pnamunn/Lunabotics/CAD/HADES CAD/Chassis/Copy of Motor Casing Bottom.SLDPRT

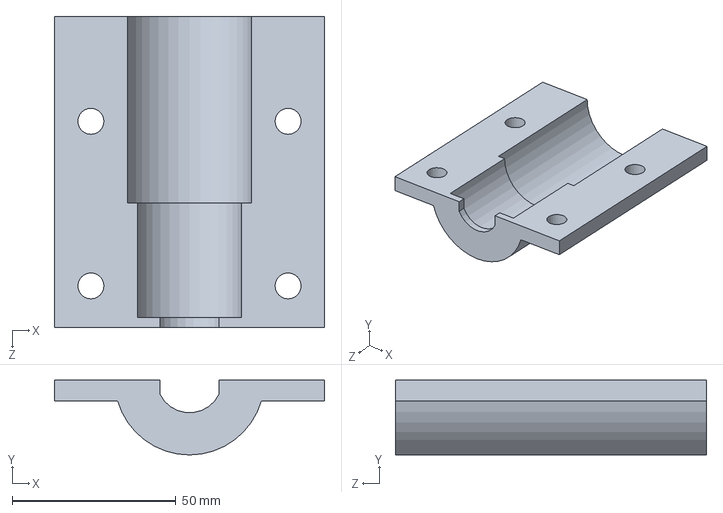
[picture p14: CAD file, 2023-11-08]
CAD/HADES CAD/Chassis/Copy of Motor Casing Bottom.SLDPRT
82.5 x 22.9 x 94.9 mm
