pnamunn/Lunabotics/CAD/HADES CAD/Excavation/Acuator Sleeve.SLDPRT

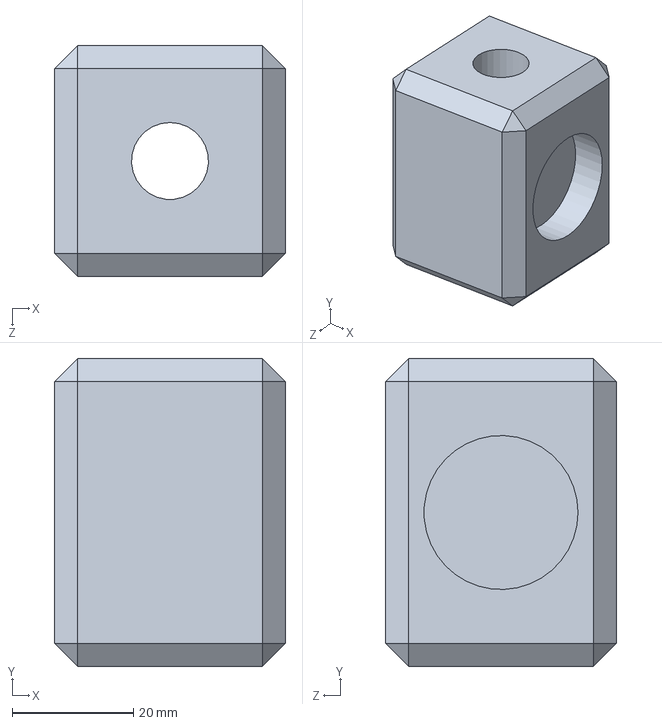
[picture p15: CAD file, 2023-11-08]
CAD/HADES CAD/Excavation/Acuator Sleeve.SLDPRT
38.1 x 50.8 x 38.1 mm
