pnamunn/Lunabotics/CAD/Wield Excavation Trial/2ft-9056K512_Multipurpose 6061 Aluminum Round Tube.SLDPRT

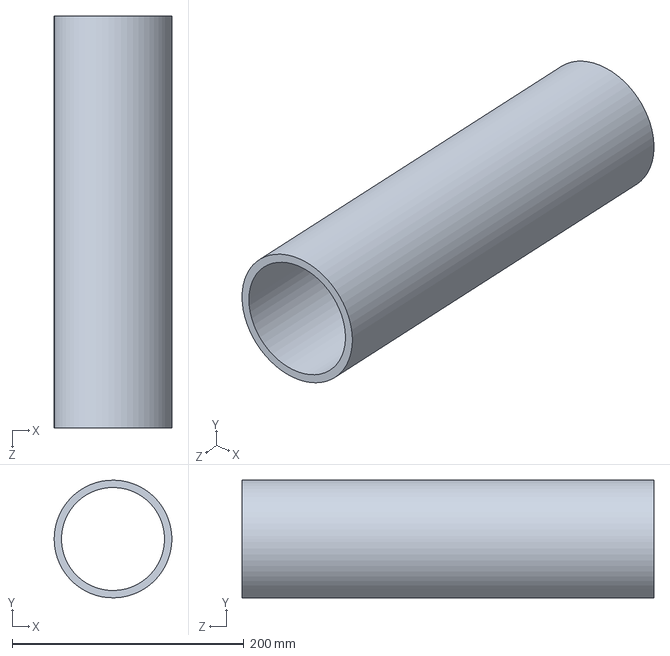
[picture p16: CAD file, 2023-11-10]
CAD/Wield Excavation Trial/2ft-9056K512_Multipurpose 6061 Aluminum Round Tube.SLDPRT
101.6 x 101.6 x 355.6 mm
