pnamunn/Lunabotics/CAD/GrouserWheel/Grouser.SLDPRT

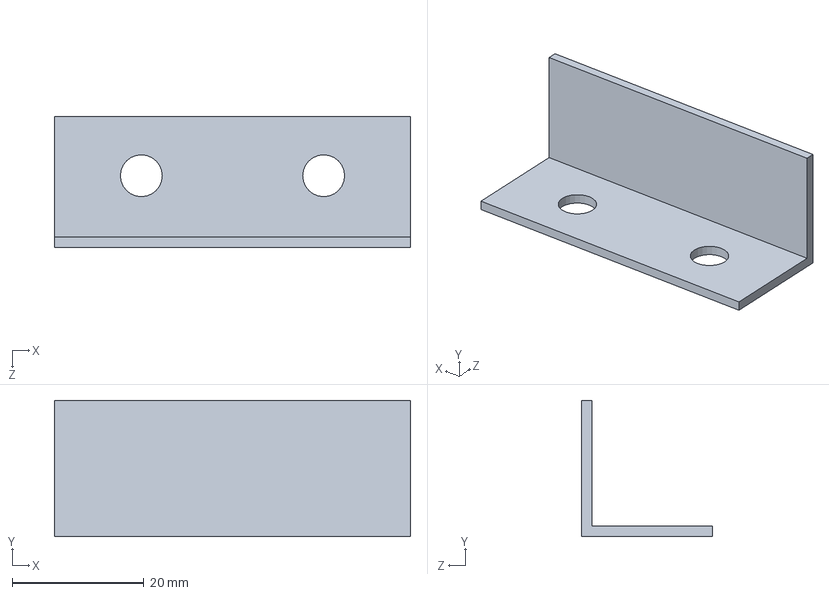
[picture p17: CAD file, 2023-10-27]
CAD/GrouserWheel/Grouser.SLDPRT
54.0 x 20.6 x 19.8 mm
