pnamunn/Lunabotics/CAD/HADES CAD/Excavation/Fixed Rod Seperator.SLDPRT

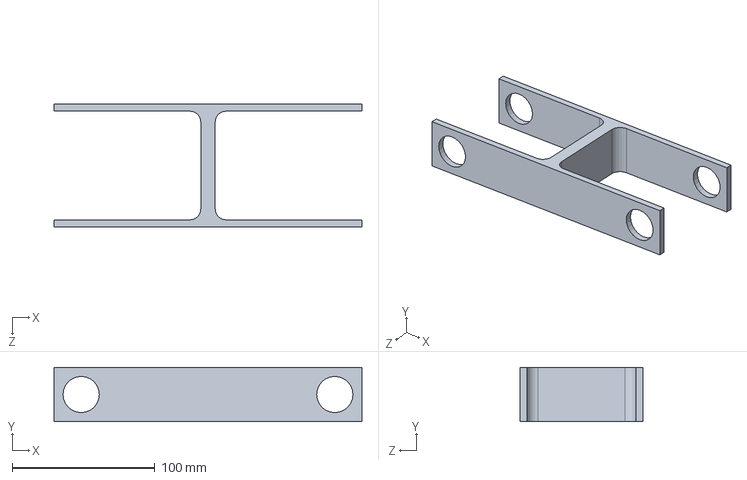
[picture p18: CAD file, 2023-11-08]
CAD/HADES CAD/Excavation/Fixed Rod Seperator.SLDPRT
215.9 x 38.1 x 86.4 mm
