pnamunn/Lunabotics/CAD/GrouserWheel/18Grouser Wheel/Grouser Wheel 20Degree.SLDPRT

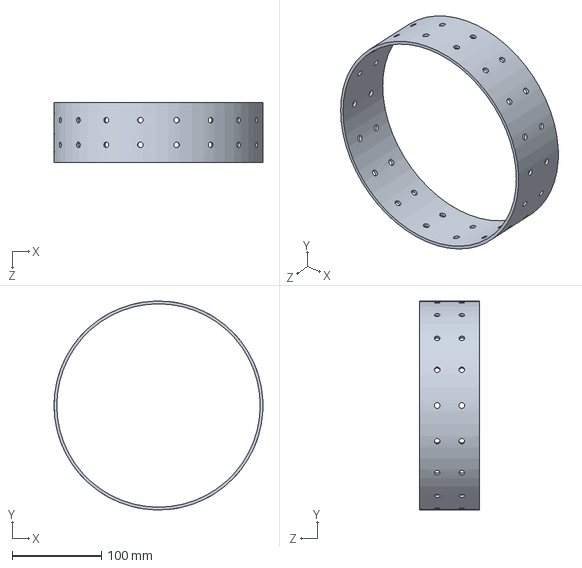
[picture p19: CAD file, 2023-11-10]
CAD/GrouserWheel/18Grouser Wheel/Grouser Wheel 20Degree.SLDPRT
233.8 x 233.7 x 66.7 mm
