pnamunn/Lunabotics/CAD/HADES CAD/Excavation/scoop.SLDPRT

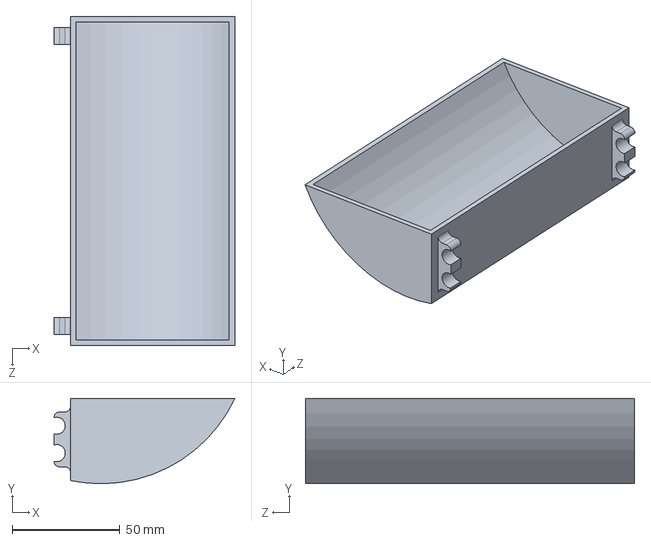
[picture p20: CAD file, 2023-11-08]
CAD/HADES CAD/Excavation/scoop.SLDPRT
83.8 x 39.5 x 152.4 mm
