pnamunn/Lunabotics/CAD/GrouserWheel/18Grouser Wheel/Wheel Mount.SLDPRT

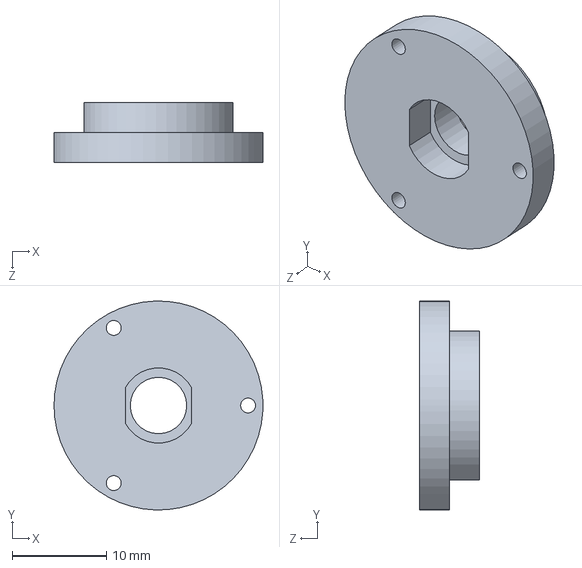
[picture p21: CAD file, 2023-10-27]
CAD/GrouserWheel/18Grouser Wheel/Wheel Mount.SLDPRT
22.2 x 22.2 x 6.36 mm
