pnamunn/Lunabotics/CAD/HADES CAD/Deposition/Deposition Spill Chute.SLDPRT

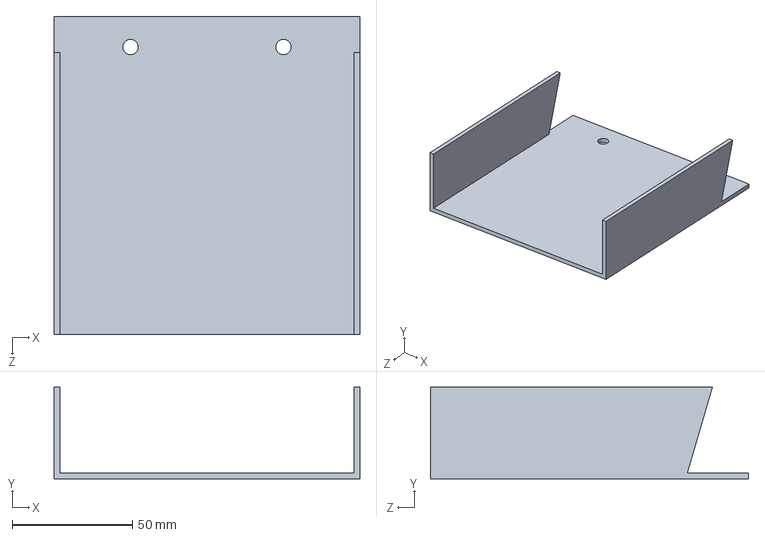
[picture p22: CAD file, 2023-11-08]
CAD/HADES CAD/Deposition/Deposition Spill Chute.SLDPRT
127.0 x 38.1 x 132.1 mm
