pnamunn/Lunabotics/CAD/HADES CAD/Drivetrain/Spoke_Standoff.SLDPRT

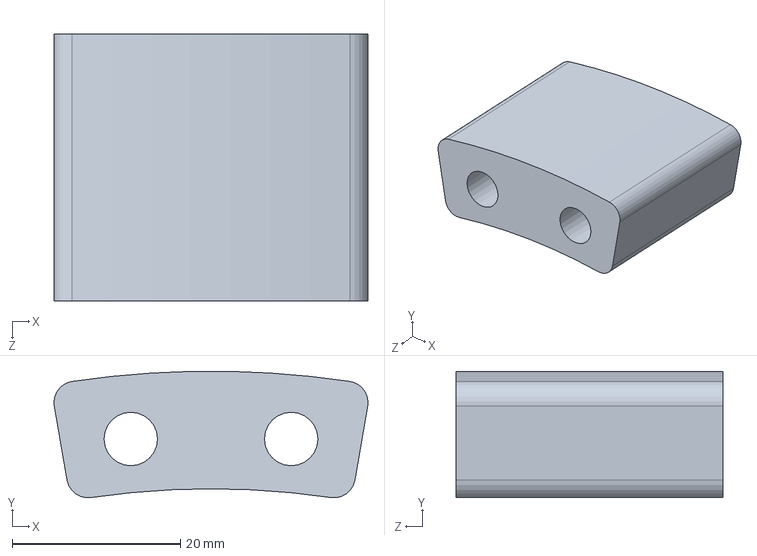
[picture p23: CAD file, 2023-11-08]
CAD/HADES CAD/Drivetrain/Spoke_Standoff.SLDPRT
37.3 x 15.0 x 31.8 mm
