pnamunn/Lunabotics/CAD/HADES CAD/Excavation/Side_Panel.SLDPRT

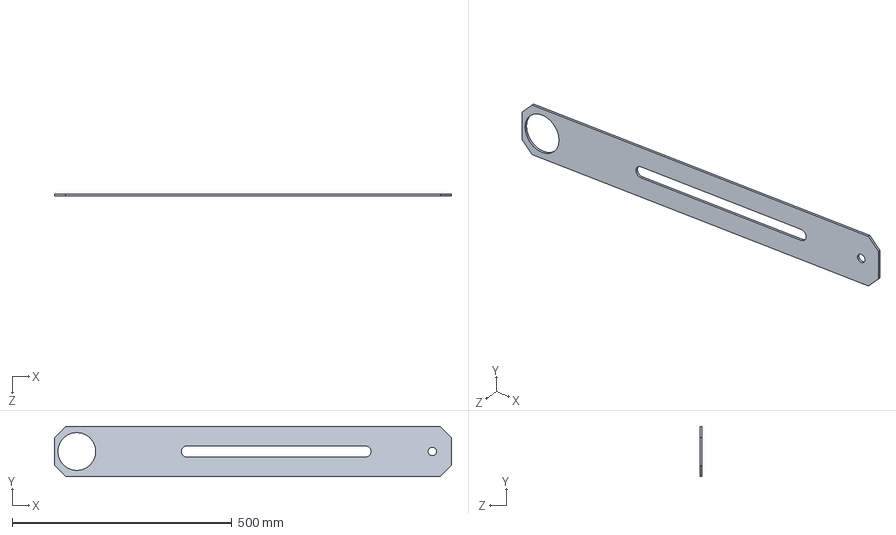
[picture p24: CAD file, 2023-11-08]
CAD/HADES CAD/Excavation/Side_Panel.SLDPRT
904.2 x 114.3 x 5.08 mm
