pnamunn/Lunabotics/CAD/GrouserWheel/18Grouser Wheel/MotorForWheel.SLDPRT

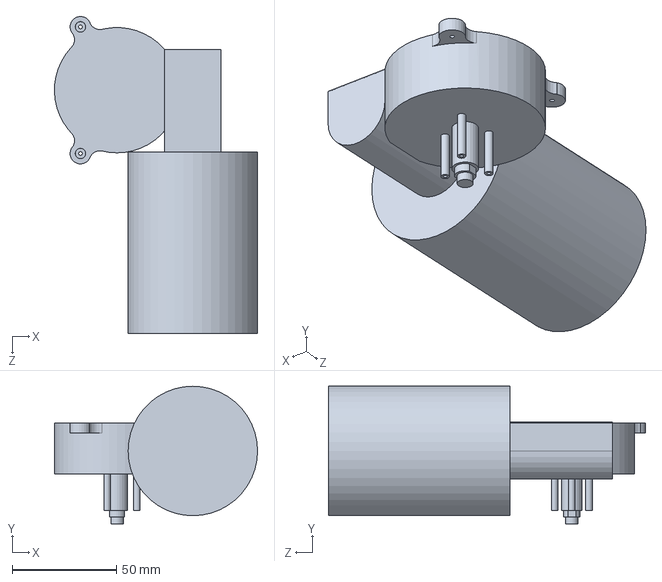
[picture p25: CAD file, 2023-10-27]
CAD/GrouserWheel/18Grouser Wheel/MotorForWheel.SLDPRT
97.3 x 65.9 x 151.8 mm
