pnamunn/Lunabotics/CAD/HADES CAD/Excavation/Fixing Rod.SLDPRT

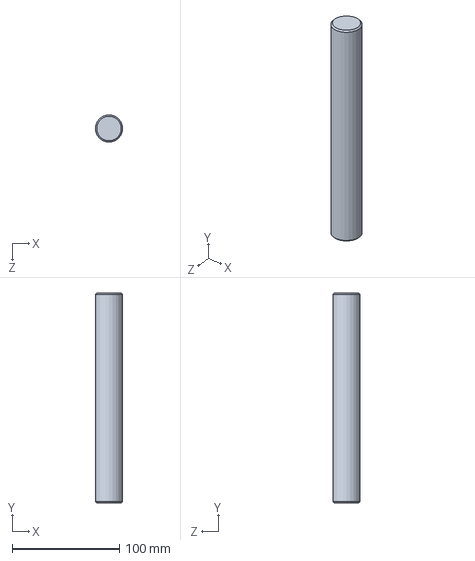
[picture p26: CAD file, 2023-11-08]
CAD/HADES CAD/Excavation/Fixing Rod.SLDPRT
25.4 x 195.6 x 25.4 mm
