pnamunn/Lunabotics/CAD/HADES CAD/Chassis/Copy of 47065T149_T-Slotted Framing.SLDPRT

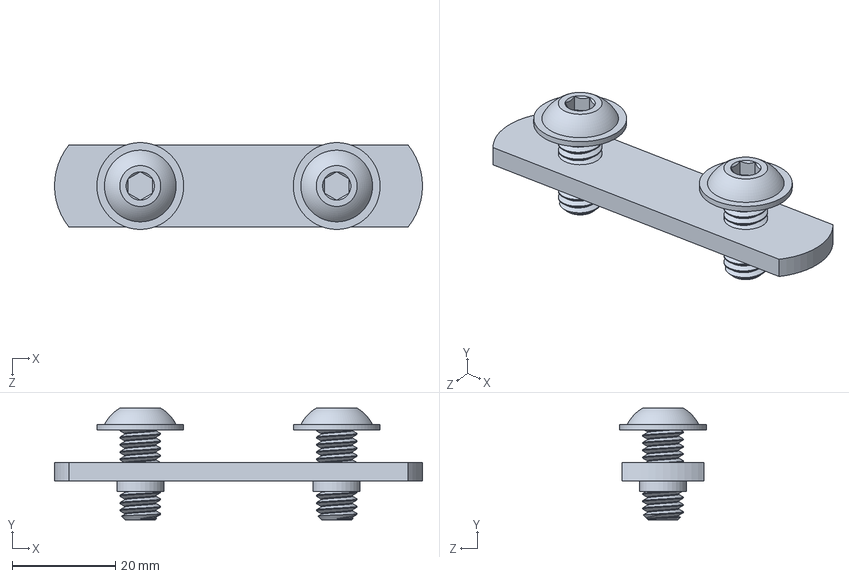
[picture p27: CAD file, 2023-11-08]
CAD/HADES CAD/Chassis/Copy of 47065T149_T-Slotted Framing.SLDPRT
71.4 x 21.7 x 16.8 mm
