pnamunn/Lunabotics/CAD/HADES CAD/Deposition/Deposition Bin Bottom.SLDPRT

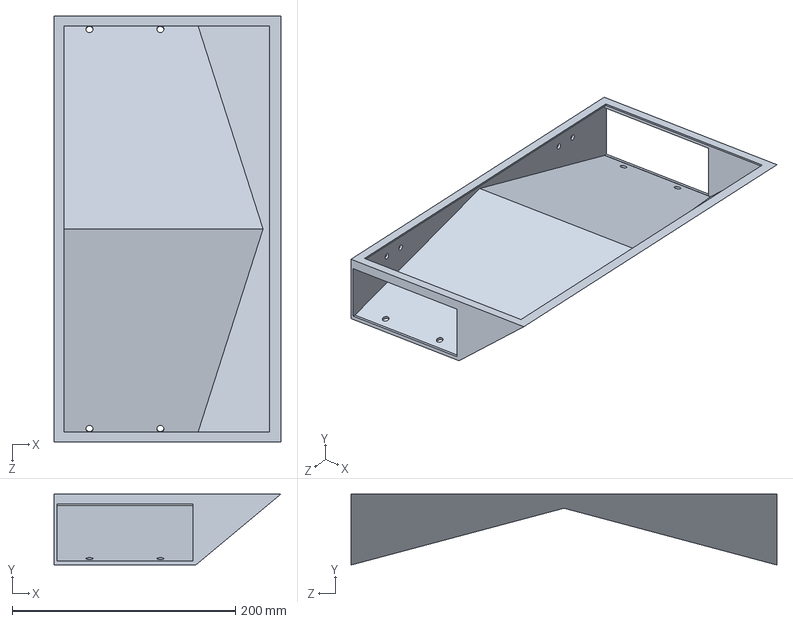
[picture p28: CAD file, 2023-11-08]
CAD/HADES CAD/Deposition/Deposition Bin Bottom.SLDPRT
203.2 x 63.5 x 381.0 mm
