pnamunn/Lunabotics/CAD/HADES CAD/Chassis/Copy of 47065T601_T-Slotted Framing.SLDPRT

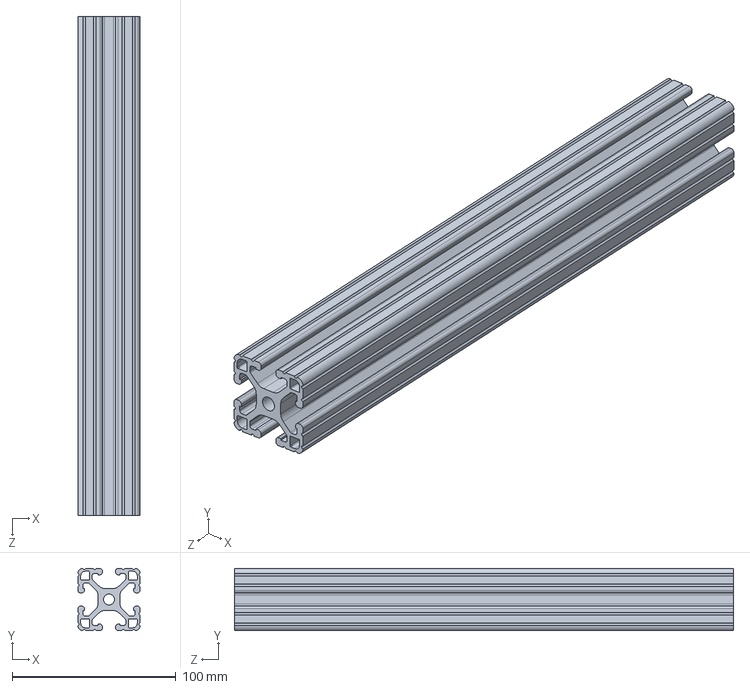
[picture p29: CAD file, 2023-11-08]
CAD/HADES CAD/Chassis/Copy of 47065T601_T-Slotted Framing.SLDPRT
38.1 x 38.1 x 304.8 mm
