pnamunn/Lunabotics/CAD/HADES CAD/Deposition/Deposition Bin Top.SLDPRT

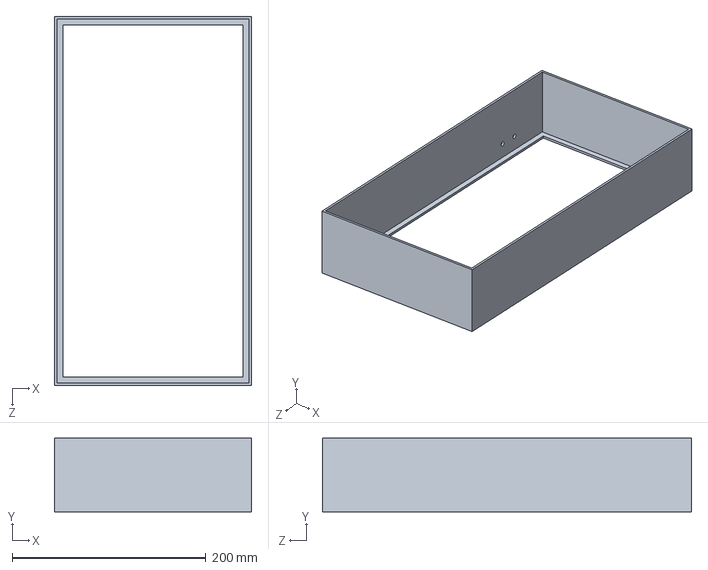
[picture p30: CAD file, 2023-11-08]
CAD/HADES CAD/Deposition/Deposition Bin Top.SLDPRT
203.2 x 76.2 x 381.0 mm
