pnamunn/Lunabotics/CAD/HADES CAD/Drivetrain/Motor Mounting Hub.SLDPRT

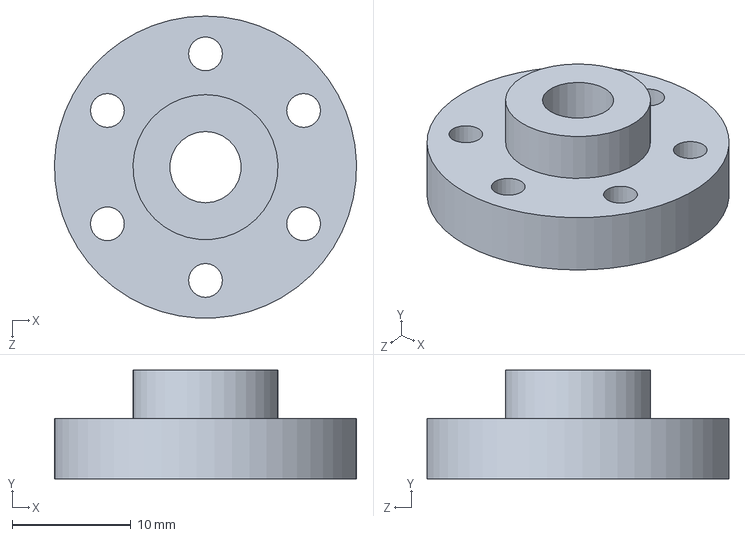
[picture p31: CAD file, 2023-11-08]
CAD/HADES CAD/Drivetrain/Motor Mounting Hub.SLDPRT
25.4 x 9.14 x 25.4 mm
