pnamunn/Lunabotics/CAD/HADES CAD/Excavation/Linear Actuator.SLDPRT

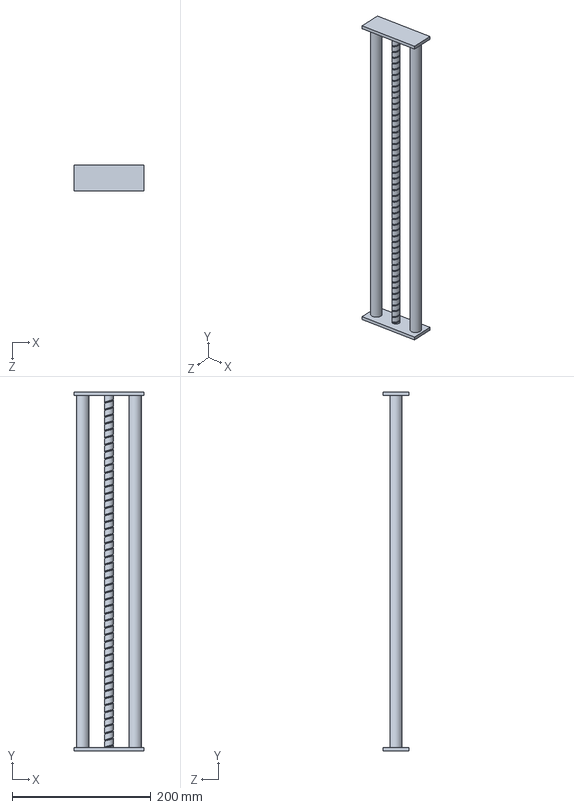
[picture p32: CAD file, 2023-11-08]
CAD/HADES CAD/Excavation/Linear Actuator.SLDPRT
101.6 x 518.2 x 38.1 mm
