pnamunn/Lunabotics/CAD/HADES CAD/Chassis/Copy of 47065T241_Silver Corner Bracket.SLDPRT

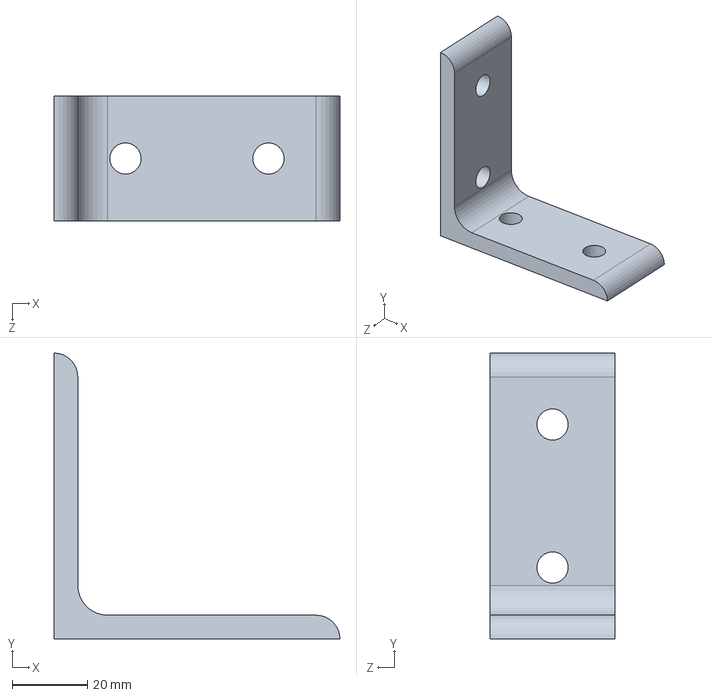
[picture p33: CAD file, 2023-11-08]
CAD/HADES CAD/Chassis/Copy of 47065T241_Silver Corner Bracket.SLDPRT
76.2 x 76.2 x 33.3 mm
