pnamunn/Lunabotics/CAD/HADES CAD/Chassis/Copy of 3136N275_T-Slotted Framing.SLDPRT

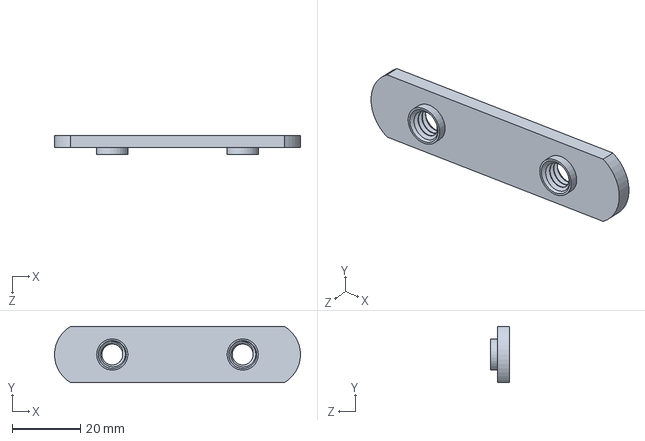
[picture p34: CAD file, 2023-11-08]
CAD/HADES CAD/Chassis/Copy of 3136N275_T-Slotted Framing.SLDPRT
71.9 x 16.4 x 5.64 mm
