pnamunn/Lunabotics/CAD/HADES CAD/Chassis/Copy of Pivot Plate.SLDPRT

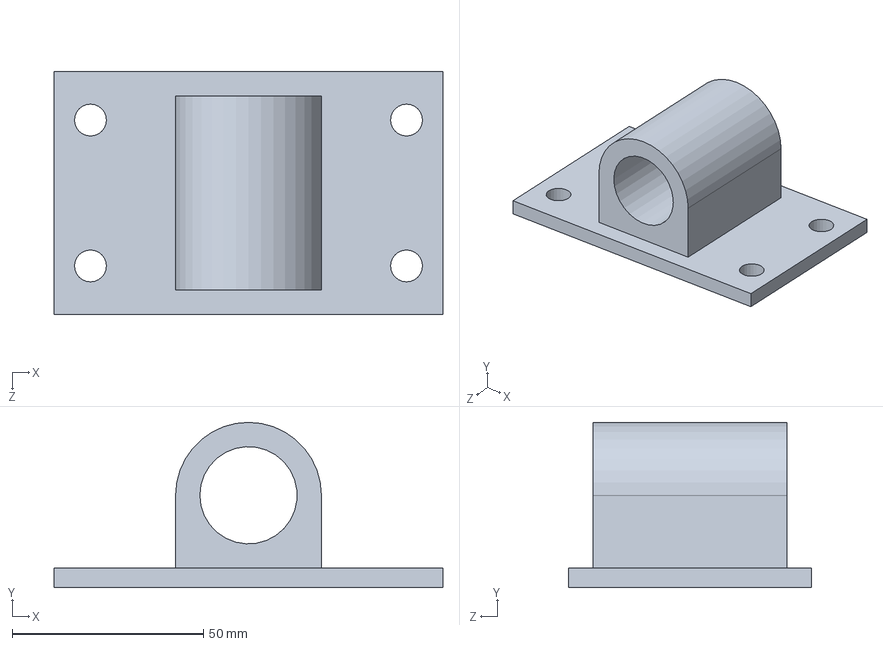
[picture p35: CAD file, 2023-11-08]
CAD/HADES CAD/Chassis/Copy of Pivot Plate.SLDPRT
101.6 x 43.2 x 63.5 mm
