pnamunn/Lunabotics/CAD/HADES CAD/Drivetrain/Motor Casing Top.SLDPRT

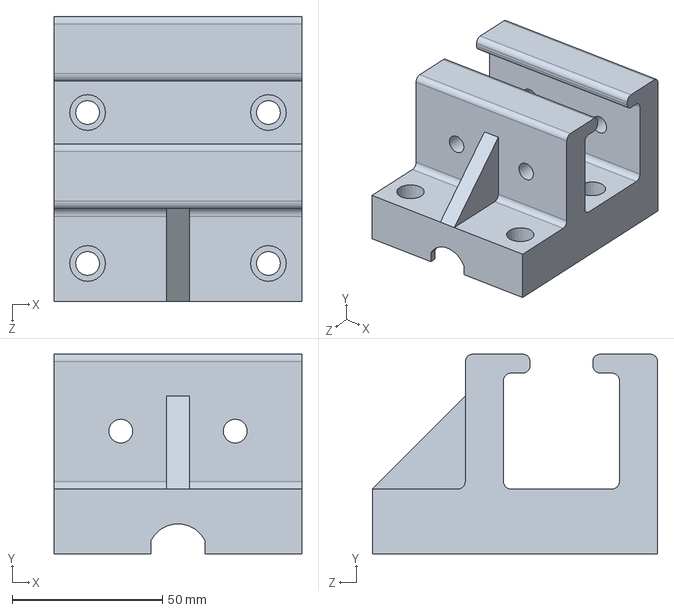
[picture p36: CAD file, 2023-11-08]
CAD/HADES CAD/Drivetrain/Motor Casing Top.SLDPRT
82.5 x 66.5 x 94.9 mm
