pnamunn/Lunabotics/CAD/HADES CAD/Drivetrain/Wheel_Spoke.SLDPRT

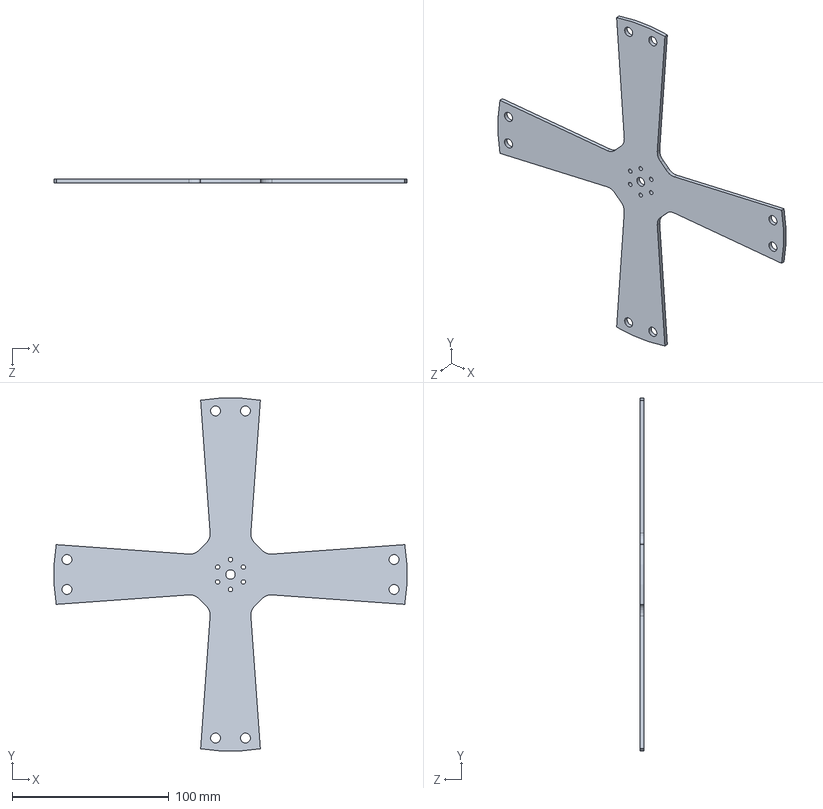
[picture p37: CAD file, 2023-11-08]
CAD/HADES CAD/Drivetrain/Wheel_Spoke.SLDPRT
225.2 x 225.2 x 2.54 mm
