pnamunn/Lunabotics/CAD/HADES CAD/Chassis/Copy of 47065T602_T-Slotted Framing.SLDPRT

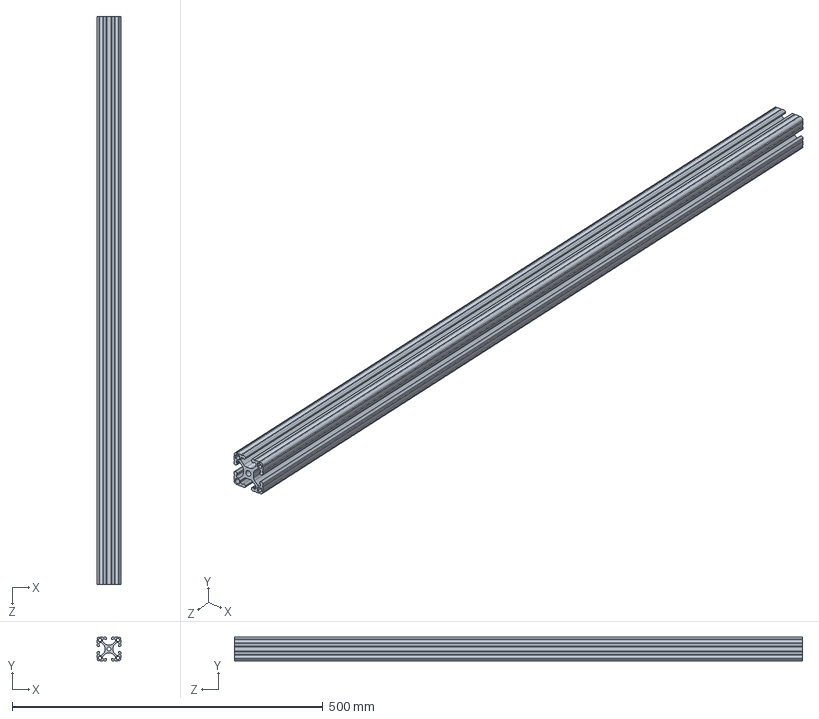
[picture p38: CAD file, 2023-11-08]
CAD/HADES CAD/Chassis/Copy of 47065T602_T-Slotted Framing.SLDPRT
38.1 x 38.1 x 914.4 mm
