pnamunn/Lunabotics/CAD/HADES CAD/Excavation/Drive_Key.SLDPRT

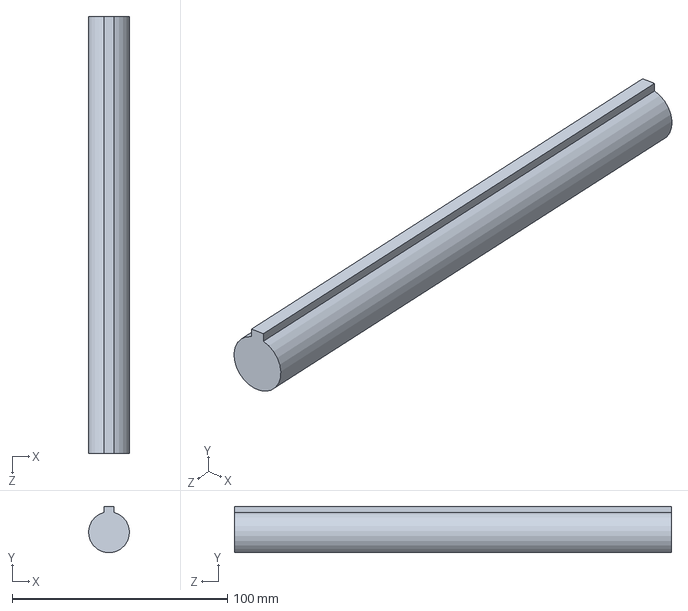
[picture p39: CAD file, 2023-11-08]
CAD/HADES CAD/Excavation/Drive_Key.SLDPRT
19.0 x 21.5 x 203.2 mm
