pnamunn/Lunabotics/CAD/HADES CAD/Drivetrain/Wheel_Fin.SLDPRT

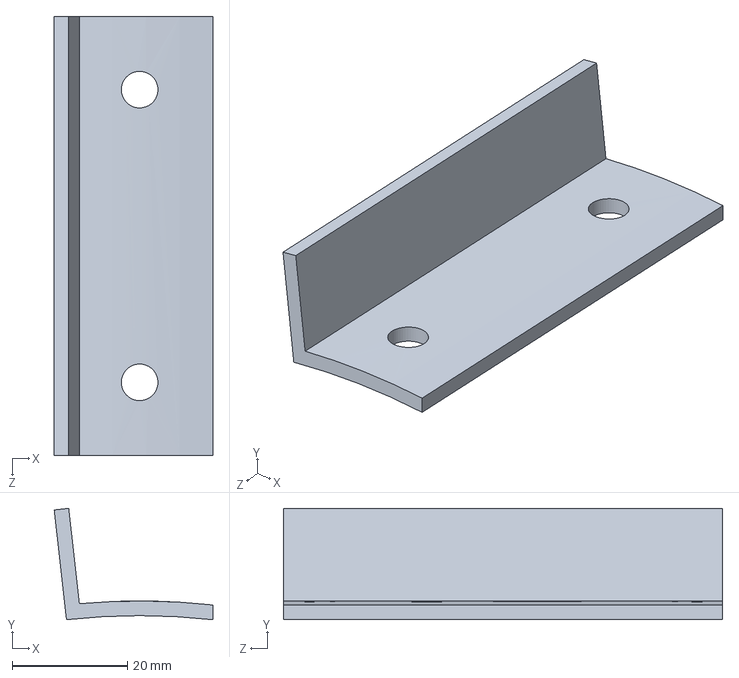
[picture p40: CAD file, 2023-11-08]
CAD/HADES CAD/Drivetrain/Wheel_Fin.SLDPRT
27.5 x 19.3 x 76.2 mm
