pnamunn/Lunabotics/CAD/HADES CAD/Chassis/Copy of Wheel_Spoke_Standoff.SLDPRT

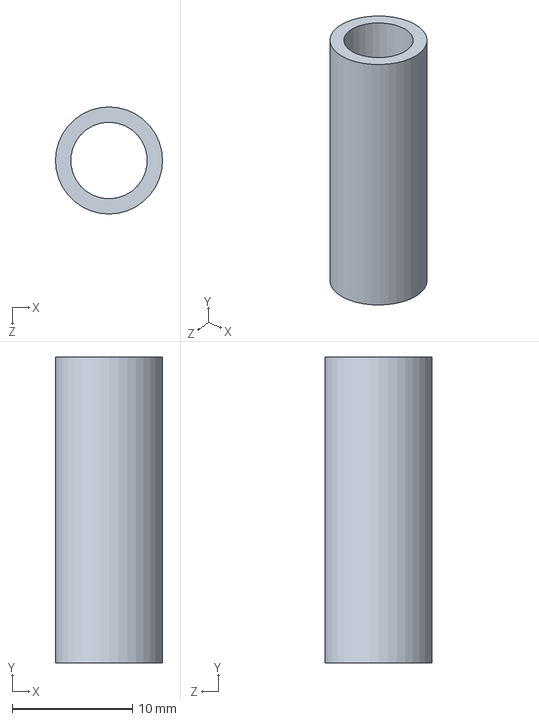
[picture p41: CAD file, 2023-11-08]
CAD/HADES CAD/Chassis/Copy of Wheel_Spoke_Standoff.SLDPRT
8.89 x 25.4 x 8.89 mm
