pnamunn/Lunabotics/CAD/HADES CAD/Chassis/Copy of 47065T962_T-Slotted Framing.SLDPRT

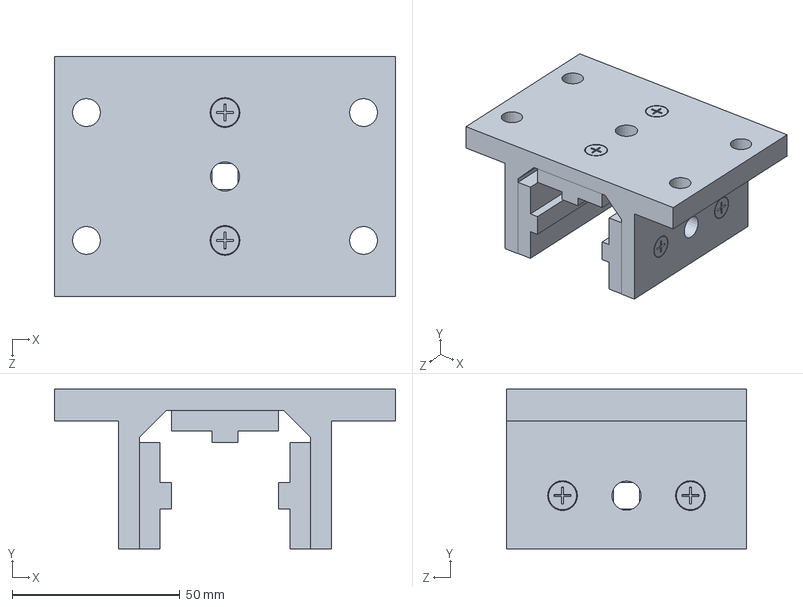
[picture p42: CAD file, 2023-11-08]
CAD/HADES CAD/Chassis/Copy of 47065T962_T-Slotted Framing.SLDPRT
101.6 x 47.6 x 71.4 mm
