pnamunn/Lunabotics/CAD/HADES CAD/Chassis/Copy of 1346K24_Rotary Shaft.SLDPRT

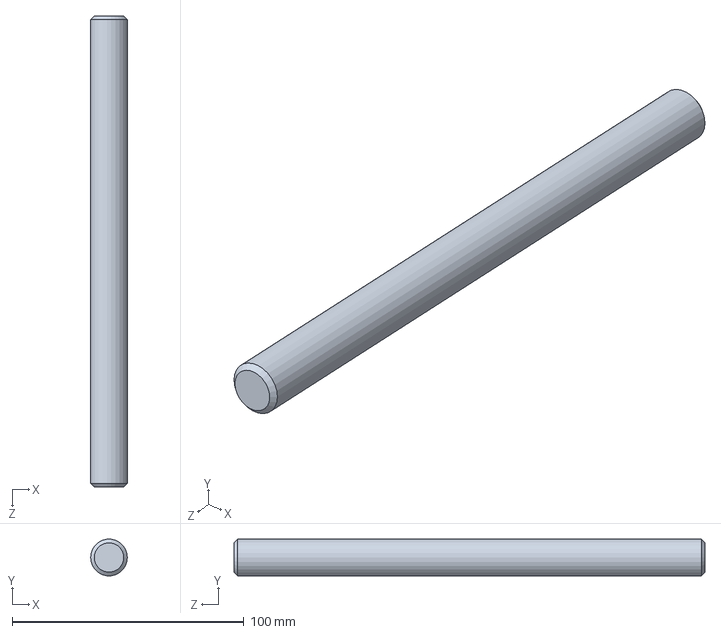
[picture p43: CAD file, 2023-11-08]
CAD/HADES CAD/Chassis/Copy of 1346K24_Rotary Shaft.SLDPRT
15.9 x 15.8 x 203.2 mm
