pnamunn/Lunabotics/CAD/HADES CAD/Chassis/Copy of 47065T853_T-Slotted Framing.SLDPRT

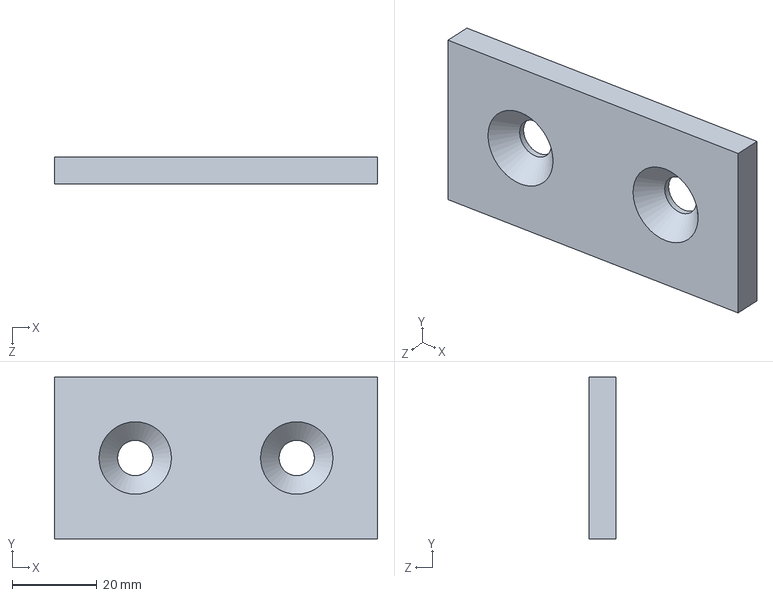
[picture p44: CAD file, 2023-11-08]
CAD/HADES CAD/Chassis/Copy of 47065T853_T-Slotted Framing.SLDPRT
76.2 x 38.1 x 6.35 mm
