pnamunn/Lunabotics/CAD/HADES CAD/Chassis/Copy of 47065T854_T-Slotted Framing.SLDPRT

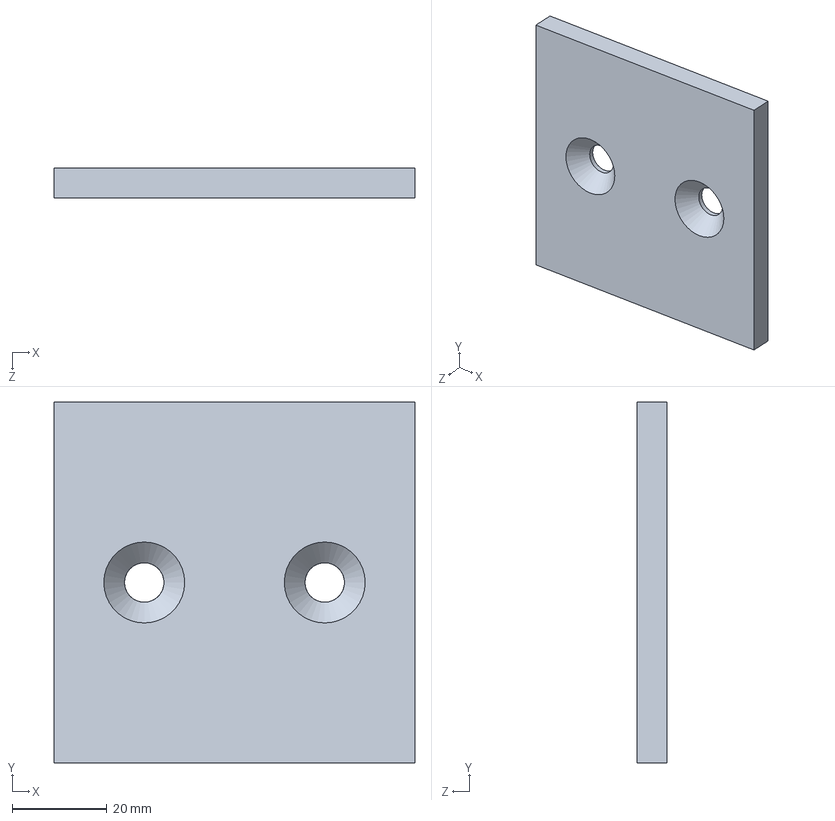
[picture p45: CAD file, 2023-11-08]
CAD/HADES CAD/Chassis/Copy of 47065T854_T-Slotted Framing.SLDPRT
76.2 x 76.2 x 6.35 mm
