pnamunn/Lunabotics/CAD/Wield Excavation Trial/WieldHelp.SLDASM

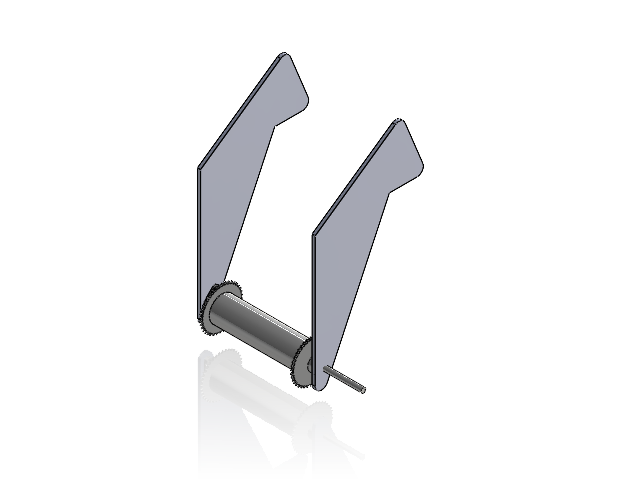
[picture p48: CAD file, 2023-11-10]
CAD/Wield Excavation Trial/WieldHelp.SLDASM
Wall Panels x 2
1497K61_1045 Carbon Steel Keyed Rotary Shaft (1)
6793K161_Steel Machinable-Bore Sprocket x 2
2ft-9056K512_Multipurpose 6061 Aluminum Round Tube
5968K73_Mounted Sealed Ball Bearing with Two-Bolt Flange (1) x 2
