pnamunn/Lunabotics/CAD/HADES CAD/Deposition/Deposition SubASM.SLDASM

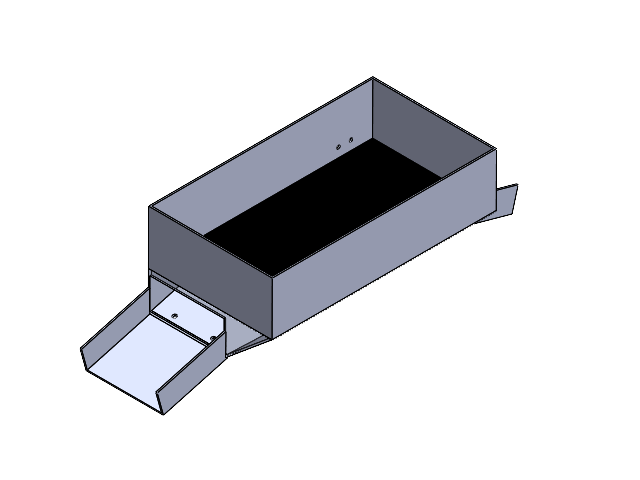
[picture p49: CAD file, 2023-11-08]
CAD/HADES CAD/Deposition/Deposition SubASM.SLDASM
Deposition Bin Bottom
Deposition Spill Chute x 2
Deposition Bin Top
85385T809_304 Stainless Steel Wire Cloth
1549A57_Strap Hinge x 2
1549A57_Strap Hinge2 x 2
