pnamunn/Lunabotics/FINAL_CODE/serial_joystick.py

''' 
Program:        serial_joystick.py
Author:         Patricia Munn

Use Case:       Runs on the Jetson Orin Nano on-board the rover.  Allows for
                communication between the user in Mission Control and the rover
                in the arena.  Takes joystick and button commands from the Logitech
                gamepad plugged into the UI laptop before processing them & 
                serially sending them to the Arduino Mega through UART, where
                they will go as PWM signals to the motors & linear actuators.

                The left joystick controls the rover's drivetrain motors & the
                buttonsmcontrol the excavation chain motormand the linear actuators.

                A joy_node must be running on the UI laptop, with the Logitech 
                F310 gamepad plugged in and flipped to D mode with the mode 
                button light off.  Both the Jetson and the laptop must be on 
                the same network for ROS2 to automatically allow communication 
                between the 2 nodes running on different devices.


Functionality:  First creates the gamepad_subber_node and sets it to subscribe
                to a joy_node's /joy topic to receive the user input data coming
                from the Logitech gamepad's joysticks and buttons.

                This code's gamepad_subber_node then constantly monitors the
                gamepad input coming from the joy_node and will process and send
                new commands if they come.  If the left joystick moves outside the
                deadzone, it's x & y axis values are translated to the proper
                direction/speed and normalized to the Arduino's PWM range of
                [3999, 1999] in the arcade_drive() function.  The duty values are
                sent serially as 4 bytes with 1 message type byte.
                The button values are sent as 1 byte with 3 useless filler bytes
                and 1 message type byte.


Documentation   rclpy library   https://docs.ros2.org/foxy/api/rclpy/
used:           Joy sensor_msgs   https://docs.ros2.org/foxy/api/sensor_msgs/msg/Joy.html
                Pyserial library   https://pyserial.readthedocs.io/en/latest/pyserial_api.html#classes
                Arcade Drive Interactive Quadrants   https://xiaoxiae.github.io/Robotics-Simplified-Website/drivetrain-control/arcade-drive/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)-,Visualization,-Here%20is%20an
                Exponential Arcade Drive Math   https://www.desmos.com/calculator/i6en4qtdwg
'''

import serial
import rclpy
from rclpy.node import Node
from sensor_msgs.msg import Joy
from bitarray import bitarray
import time


class GamepadSubber(Node):      # node that subs to /joy pubber

    def __init__(self):     # Constructor

        super().__init__('gamepad_subber_node')  

        ''' Creates a subber node of msg_type=Joy, topic_name=joy, callback_function=joy_callback() '''
        self.subber = self.create_subscription(Joy, 'joy', self.joy_callback, 10)

        self.get_logger().info("GamepadSubber(Node) instance created.")
        self.ser = serial.Serial('/dev/ttyACM0', 500000, bytesize=8, timeout=2)      # serial to Arduino Mega

        self._deadzone = 0.1

        self.curr_joy = [0, 0]  # holds left & right motor vals
        self.last_joy = [0, 0] 

        # self.curr_gimb = [0, 0]  # holds left & right gimble vals
        # self.last_gimb = [0, 0]

        self.last_butt = bytearray([0, 0, 0, 0, 0, 0, 0, 0])   # holds self.button_values array

        self.left_motor = 0
        self.right_motor = 0

        # self.left_gimble = 0
        # self.right_gimble = 0


    def send(self, cmd):        # Used to serial Tx
        if (type(cmd) == str):
            self.ser.write(cmd.encode())
        elif (type(cmd) == bytes):
            self.ser.write(cmd)
        time.sleep(0.05)    # small delay to prevent data overrun in small Arduino Rx buffer


    def send_duty_vals(self):

        self.curr_joy[0] = self.left_motor
        self.curr_joy[1] = self.right_motor

        right_low = (self.right_motor & 0b0000_0000_1111_1111)
        right_high = (self.right_motor >> 8)
        left_low = (self.left_motor & 0b0000_0000_1111_1111)
        left_high = (self.left_motor >> 8)


        if (self.curr_joy != self.last_joy):

            if (self.left_motor == 2999 and self.right_motor == 2999):
                self.get_logger().info(f' L deadzone')
            else:
                self.get_logger().info(f' L joystick moving')
        
            self.send(b'2')                      # send message_type 2
            self.send((left_high).to_bytes(1, byteorder="big"))
            self.send((left_low).to_bytes(1, byteorder="big"))
            self.send((right_high).to_bytes(1, byteorder="big"))
            self.send((right_low).to_bytes(1, byteorder="big"))

            ########### output to ROS terminal ####
            self.get_logger().info(f' L Left = {self.left_motor}')
            self.get_logger().info(f' L Right = {self.right_motor}')
            # self.get_logger().info(f' lh = {format(left_high, "08b")}')
            # self.get_logger().info(f' ll = {format(left_low, "08b")}')
            # self.get_logger().info(f' rh = {format(right_high, "08b")}')
            # self.get_logger().info(f' rl = {format(right_low, "08b")}')
            ###############################################################

        self.last_joy[0] = self.left_motor
        self.last_joy[1] = self.right_motor



    # def send_gimble_vals(self):
    #     self.curr_gimb[0] = self.left_gimble
    #     self.curr_gimb[1] = self.right_gimble

    #     right_gimb_low = (self.right_gimble & 0b0000_0000_1111_1111)
    #     right_gimb_high = (self.right_gimble >> 8)
    #     left_gimb_low = (self.left_gimble & 0b0000_0000_1111_1111)
    #     left_gimb_high = (self.left_gimble >> 8)


    #     if (self.curr_gimb != self.last_gimb):

    #         if (self.left_gimble == 2999 and self.right_gimble == 2999):
    #             self.get_logger().info(f'R deadzone')
    #         else:
    #             self.get_logger().info(f'R joystick moving')
        
    #         self.send(b'3')     # send message_type 3
    #         time.sleep(0.05)
            
    #         self.send((left_gimb_high).to_bytes(1, byteorder="big"))
    #         time.sleep(0.05)

    #         self.send((left_gimb_low).to_bytes(1, byteorder="big"))
    #         time.sleep(0.05)

    #         self.send((right_gimb_high).to_bytes(1, byteorder="big"))
    #         time.sleep(0.05)

    #         self.send((right_gimb_low).to_bytes(1, byteorder="big"))
    #         time.sleep(0.05)

    #         ########### output to ROS terminal ####
    #         self.get_logger().info(f'R Left = {self.left_gimble}')
    #         self.get_logger().info(f'R Right = {self.right_gimble}')
    #         # self.get_logger().info(f'lh = {format(left_high, "08b")}')
    #         # self.get_logger().info(f'll = {format(left_low, "08b")}')
    #         # self.get_logger().info(f'rh = {format(right_high, "08b")}')
    #         # self.get_logger().info(f'rl = {format(right_low, "08b")}')
    #         ###############################################################

    #     self.last_gimb[0] = self.left_gimble
    #     self.last_gimb[1] = self.right_gimble



    def arcade_drive(self, behavior, x, y):
        x = -x      # Change bc gamepad's x axis is backwards

        match behavior:
            case "LINEAR":
                pass

            case "EXPONENTIAL":
                c = 0.85
                if x > 0:
                    x = self._deadzone + (c * x**3) + (((1 - self._deadzone) - c) * x)
                else:
                    x = -(self._deadzone) + (c * x**3) + (((1 - self._deadzone) - c) * x)

                y = (c * y**3) + ((1 - c) * y)      # TODO change?

            case _:
                raise ValueError("Invalid arcade_drive() behavior argument given in code")
        
        self.max = max(abs(y), abs(x))
        self.sum = y + x
        self.diff = y - x

        if y >= 0:      # if y is positive
            if x >= 0:      # if x is positive      # Quadrant 1
                self.left_motor = self.max
                self.right_motor = self.diff
            else:       # if x is negative          # Quadrant 2
                self.left_motor = self.sum
                self.right_motor = self.max

        else:   # if y is negative                  # Quadrant 4
            if x >= 0:      # if x is positive
                self.left_motor = self.sum
                self.right_motor = -(self.max)
            else:       # if x is negative          # Quadrant 3
                self.left_motor = -(self.max)
                self.right_motor = self.diff

        # print(f" L = {self.left_motor}")
        # print(f" R = {self.right_motor}")
        self.normalize_for_half_duty()



    # def linear_arcade_drive(self, x, y):
    #     x = -x      # Change bc gamepad's x axis is backwards
    #     self.max = max(abs(y), abs(x))
    #     self.sum = y + x
    #     self.diff = y - x

    #     if y >= 0:      # if y is positive
    #         if x >= 0:      # if x is positive      # Quadrant 1
    #             self.left_motor = self.max
    #             self.right_motor = self.diff
    #         else:       # if x is negative          # Quadrant 2
    #             self.left_motor = self.sum
    #             self.right_motor = self.max

    #     else:   # if y is negative                  # Quadrant 4
    #         if x >= 0:      # if x is positive
    #             self.left_motor = self.sum
    #             self.right_motor = -(self.max)
    #         else:       # if x is negative          # Quadrant 3
    #             self.left_motor = -(self.max)
    #             self.right_motor = self.diff

    #     # print(f"Linear L = {self.left_motor}")
    #     # print(f"Linear R = {self.right_motor}")
    #     self.normalize_for_half_duty()




    # def exponential_arcade_drive(self, x, y):
    #     c = 0.85
    #     x = -x      # Change bc gamepad's x axis is backwards

    #     # Exponentiates x & y before doing arcade drive math
    #     if x > 0:
    #         x = self._deadzone + (c * x**3) + (((1 - self._deadzone) - c) * x)
    #     else:
    #         x = -(self._deadzone) + (c * x**3) + (((1 - self._deadzone) - c) * x)

    #     y = (c * y**3) + ((1 - c) * y)


    #     self.max = max(abs(y), abs(x))
    #     self.sum = y + x
    #     self.diff = y - x
    #     if y >= 0:      # if y is positive
    #         if x >= 0:      # if x is positive      # Quadrant 1
    #             self.left_motor = self.max
    #             self.right_motor = self.diff
    #         else:       # if x is negative          # Quadrant 2
    #             self.left_motor = self.sum
    #             self.right_motor = self.max

    #     else:   # if y is negative                  # Quadrant 4
    #         if x >= 0:      # if x is positive
    #             self.left_motor = self.sum
    #             self.right_motor = -(self.max)
    #         else:       # if x is negative          # Quadrant 3
    #             self.left_motor = -(self.max)
    #             self.right_motor = self.diff
     
    #     # print(f"Exponential L = {self.left_motor}")
    #     # print(f"Exponential R = {self.right_motor}")
    #     self.normalize_for_half_duty()
    

    def normalize_for_half_duty(self):
        ''' Normalize motor values for the Arduino's 16 bit duty cycle values,
        but due to the ESC's max current constaints, only run these motors at half speeds maximum '''
        self.left_motor = int( (self.left_motor * 500) + 2999 ) 
        self.right_motor = int( (self.right_motor * 500) + 2999 )


    def normalize_for_full_duty(self):
        ''' Normalize motor values for the Arduino's 16 bit duty cycle values '''
        self.left_motor = int( (self.left_motor * 1000) + 2999 ) 
        self.right_motor = int( (self.right_motor * 1000) + 2999 )


    # def gimble_drive_math(self, x, y):
    #     x = -x      # Change bc gamepad's x axes are backwards
    #     self.max = max(abs(y), abs(x))
    #     self.sum = y + x
    #     self.diff = y - x

    #     if y >= 0:      # if y is positive
    #         if x >= 0:      # if x is positive      # Quadrant 1
    #             self.left_gimble = self.max
    #             self.right_gimble = self.diff
    #         else:       # if x is negative          # Quadrant 2
    #             self.left_gimble = self.sum
    #             self.right_gimble = self.max

    #     else:   # if y is negative                  # Quadrant 4
    #         if x >= 0:      # if x is positive
    #             self.left_gimble = self.sum
    #             self.right_gimble = -(self.max)
    #         else:       # if x is negative          # Quadrant 3
    #             self.left_gimble = -(self.max)
    #             self.right_gimble = self.diff

    #     ''' Normalize motor values for the Arduino's 16 bit duty cycle values '''
    #     self.left_gimble = int( (self.left_gimble * 1000) + 2999 )
    #     self.right_gimble = int( (self.right_gimble * 1000) + 2999 ) 




    def joy_callback(self, msg):
        ''' Callback function grabs some of the values being published by /joy topic and sends serially to Arduino. '''

        self.button_values = msg.buttons
        self.button_values.pop(11)      # gets last 4 unused buttons out of the array so button values is a 8 element array
        self.button_values.pop(10)
        self.button_values.pop(9)
        self.button_values.pop(8)
        self.button_values = bitarray(self.button_values)      # converts array into a byte array

        self.axes_values = msg.axes

        ''' Motor control using the left joystick '''
        # If left joystick is outside of deadzone
        if (self.axes_values[0] > self._deadzone or self.axes_values[0] < -(self._deadzone) or self.axes_values[1] > self._deadzone or self.axes_values[1] < -(self._deadzone)):
            self.arcade_drive("LINEAR", self.axes_values[0], self.axes_values[1])        # calc left and right motor values
            self.send_duty_vals()

        # if left joystick is within deadzone
        else:       
            self.left_motor = 2999
            self.right_motor = 2999
            self.send_duty_vals()


        # ''' Gimble control using the right joystick '''
        # # If right joystick is outside of deadzone
        # if (self.axes_values[2] > self._deadzone or self.axes_values[2] < -(self._deadzone) or self.axes_values[3] > self._deadzone or self.axes_values[3] < -(self._deadzone)):
        #     self.gimble_drive_math(self.axes_values[2], self.axes_values[3])    # calc left and right motor values
        #     self.send_gimble_vals()

        # # if right joystick is within deadzone
        # else:       
        #     self.left_gimble = 2999
        #     self.right_gimble = 2999
        #     self.send_gimble_vals()
        

        ''' Button controls '''
        if (self.last_butt != self.button_values):
            self.send(b'1')                              # send message_type 1
            self.send(bytes(self.button_values))       # converts bit array to byte and sends
            self.send(b'0')                              # send filler bytes
            self.send(b'0')
            self.send(b'0')
            
            # self.get_logger().info(f' Vals: {self.button_values}')
            # self.get_logger().info(f' Sent: {bytes(self.button_values)}')

        self.last_butt = self.button_values



def main(args=None):
    
    rclpy.init(args=args)       # inits rclpy library

    subber = GamepadSubber()    # creates a node instance

    #   Joseph Addition
    #       Easier to change python than embedded on short timescale
    #       Irregular right side motor movements, unmeasured on scope
    #           but correlated to JoyNode connection time and not idle
    #       If this runs underneath JoyNode:
    #           - Stall for a sec to collect weird stuff or a few messages in buffer
    #           - Clear that buffer
    #           - In theory garbage and desynchronization can occur as intended if
    #               garbage in the buffer or some weird pyserial thing was the issue
    time.sleep((25.0/1000.0))          
    subber.ser.reset_output_buffer()   
    # END Joseph addition

    # Initialize to stop
    subber.left_motor = 2999
    subber.right_motor = 2999
    subber.send_duty_vals()

    # subber.left_gimble = 2999
    # subber.right_gimble = 2999
    # subber.send_gimble_vals()   

    #   Joseph Addition
    #       - Ensure output is properly flushed
    time.sleep((25.0/1000.0))
    subber.ser.reset_output_buffer()
    # END Joseph addition


    rclpy.spin(subber)       # spins node (endlessly loops) until the user kills the node program (with Ctrl+C)

    subber.destroy_node()   
    rclpy.shutdown()
    subber.ser.close()


if __name__ == '__main__':
    main()
